sublunarspace/pocketpsithemius/hardware/components/3352T-1-103LF.jpg

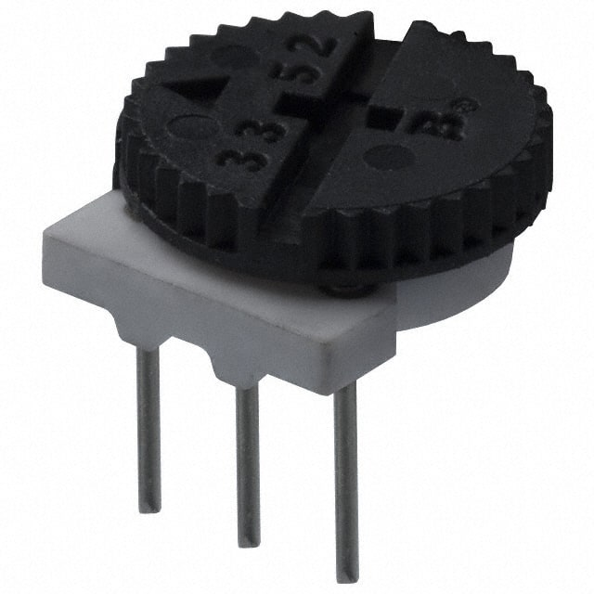
hardware/components/3352T-1-103LF.jpg
