sublunarspace/pocketpsithemius/hardware/components/7761.jpg

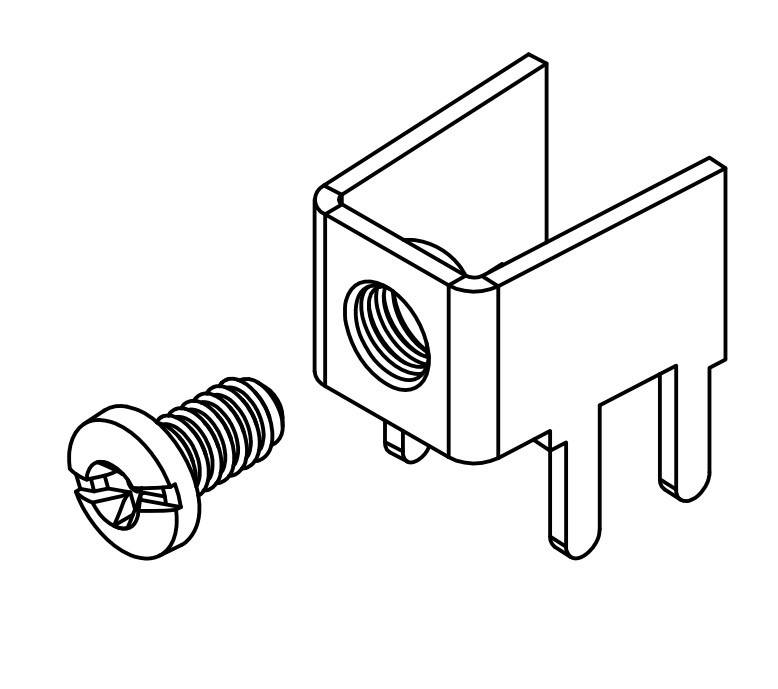
hardware/components/7761.jpg
