sublunarspace/pocketpsithemius/hardware/components/156125M173000.jpg

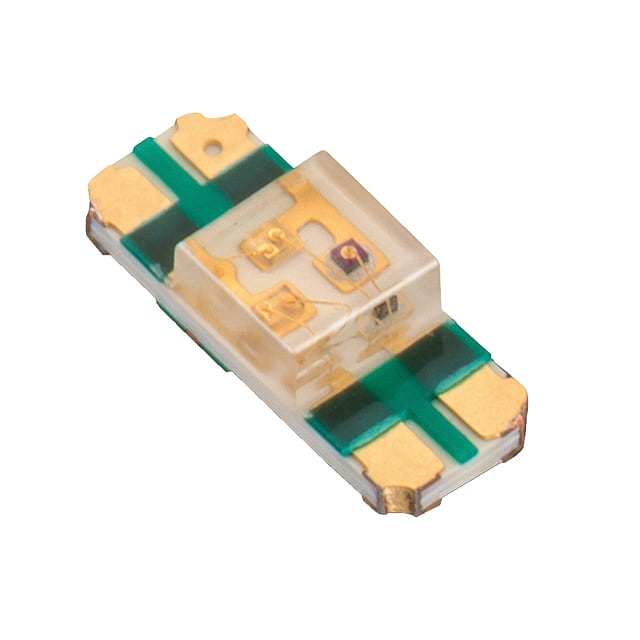
hardware/components/156125M173000.jpg
