sublunarspace/pocketpsithemius/hardware/components/61200621721.jpg

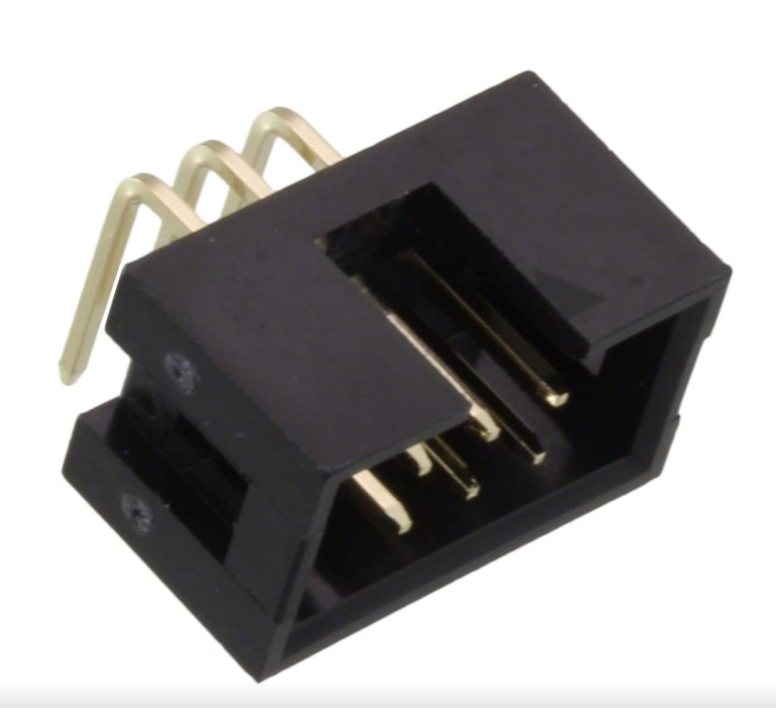
hardware/components/61200621721.jpg
