sublunarspace/pocketpsithemius/hardware/components/ATTINY84-20PU.jpg

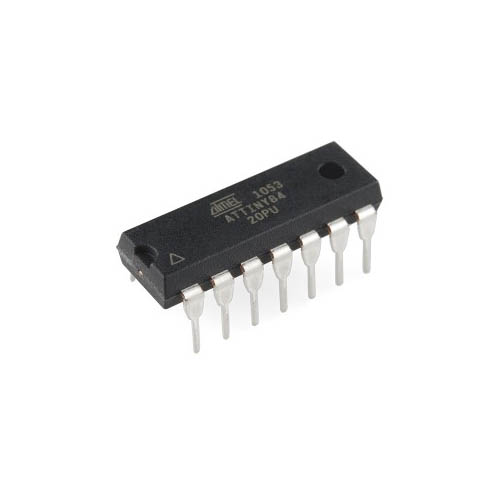
hardware/components/ATTINY84-20PU.jpg
