sublunarspace/pocketpsithemius/hardware/components/B3F-4050.jpg

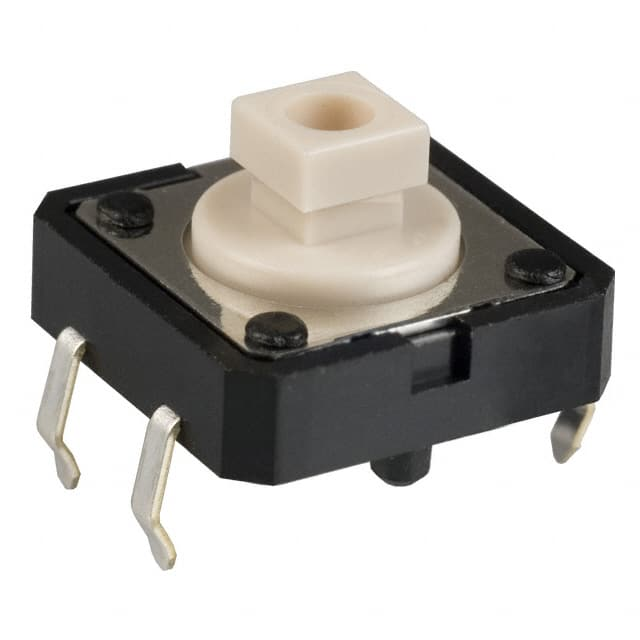
hardware/components/B3F-4050.jpg
