sublunarspace/pocketpsithemius/hardware/components/JS202011AQN.jpg

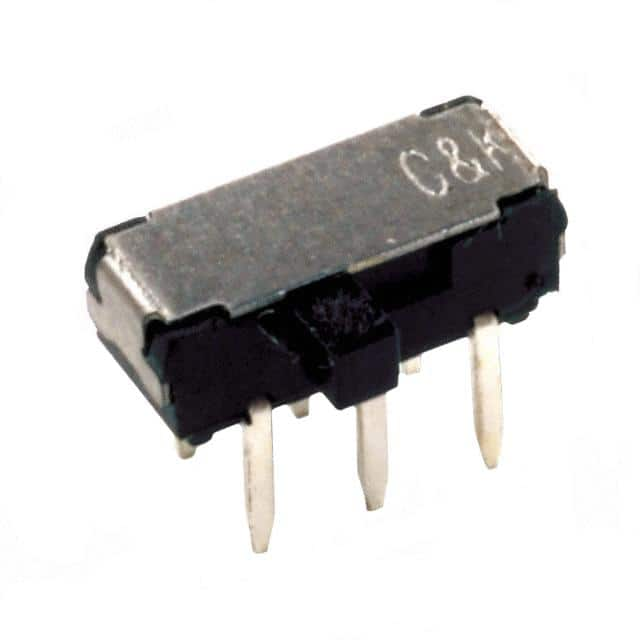
hardware/components/JS202011AQN.jpg
