sublunarspace/pocketpsithemius/hardware/components/LM386MX-1.jpg

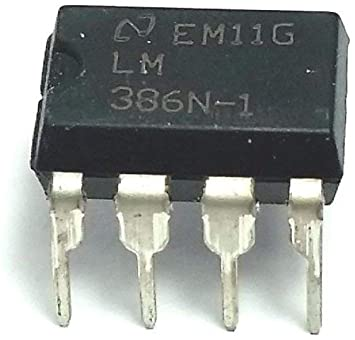
hardware/components/LM386MX-1.jpg
