sublunarspace/pocketpsithemius/hardware/components/PJ-051AH.jpg

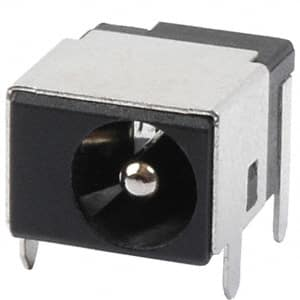
hardware/components/PJ-051AH.jpg
