sublunarspace/pocketpsithemius/hardware/components/S4B-PH-K-S(LF)(SN).jpg

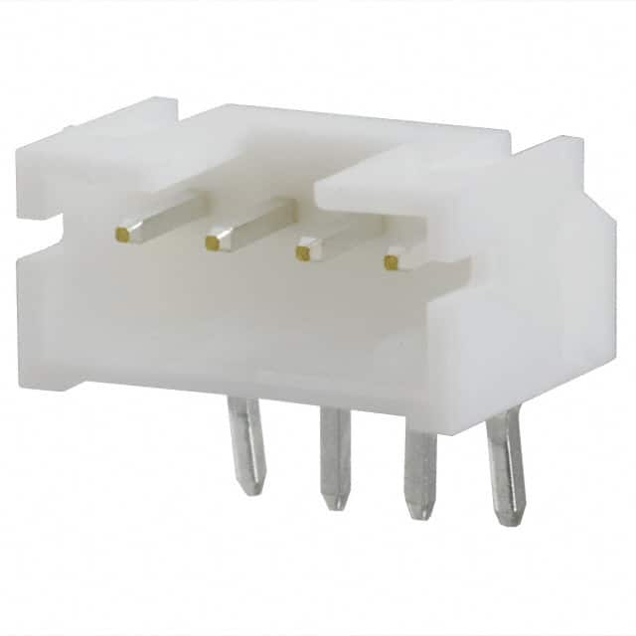
hardware/components/S4B-PH-K-S(LF)(SN).jpg
