sublunarspace/pocketpsithemius/hardware/components/TLP222A-2(F).jpg

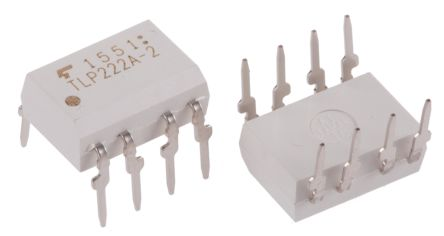
hardware/components/TLP222A-2(F).jpg
