sublunarspace/pocketpsithemius/hardware/components/TLP4227GF.jpg

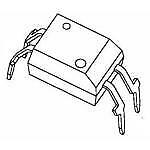
hardware/components/TLP4227GF.jpg
