sublunarspace/pocketpsithemius/hardware/components/USR1C221MDD.jpg

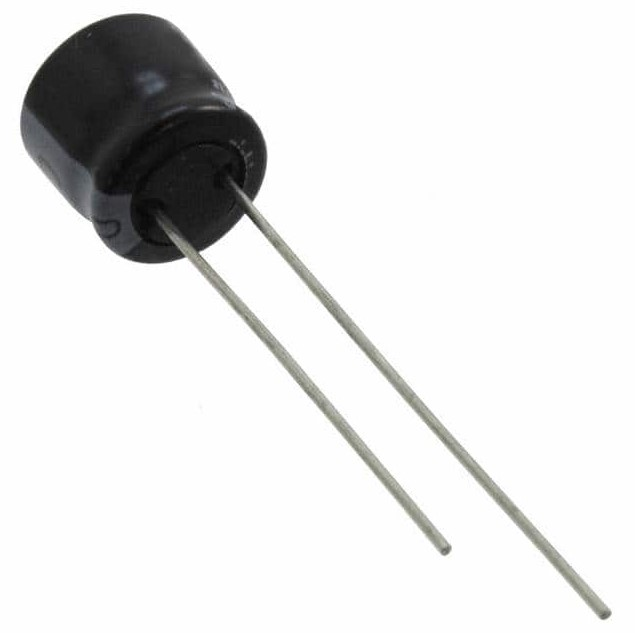
hardware/components/USR1C221MDD.jpg
