sublunarspace/pocketpsithemius/hardware/components/USV1C100MFD.jpg

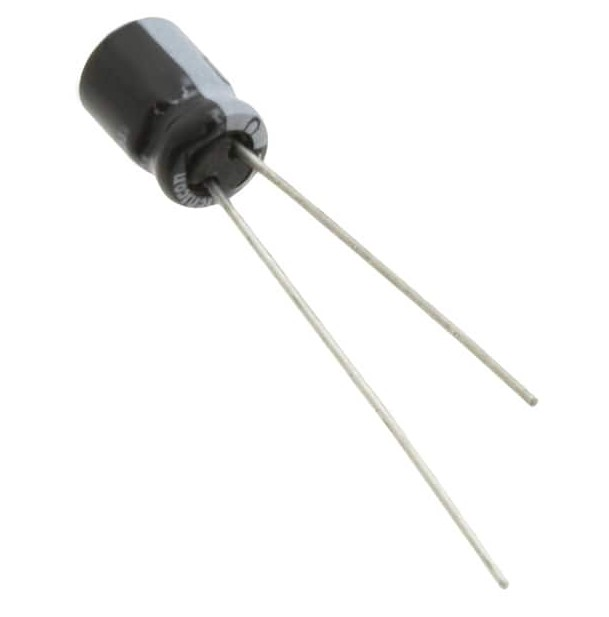
hardware/components/USV1C100MFD.jpg
