sublunarspace/pocketpsithemius/hardware/components/VAOL-5GUV8T4.jpg

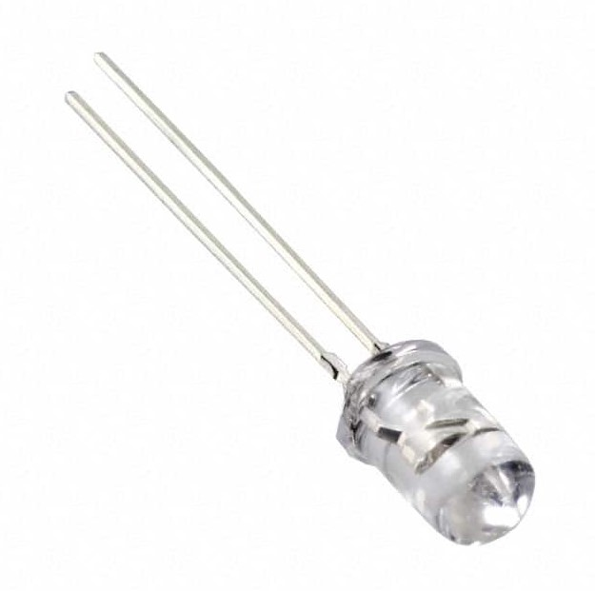
hardware/components/VAOL-5GUV8T4.jpg
