sublunarspace/pocketpsithemius/hardware/components/WW1AFT4R00.jpg

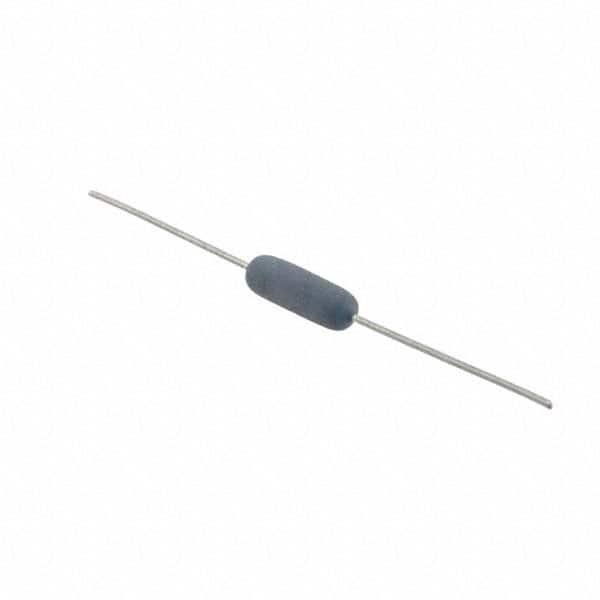
hardware/components/WW1AFT4R00.jpg
